NewTec-GmbH/esp32-can-iot/Coding/fw/doc/Media/EnvironmentDiagram.png

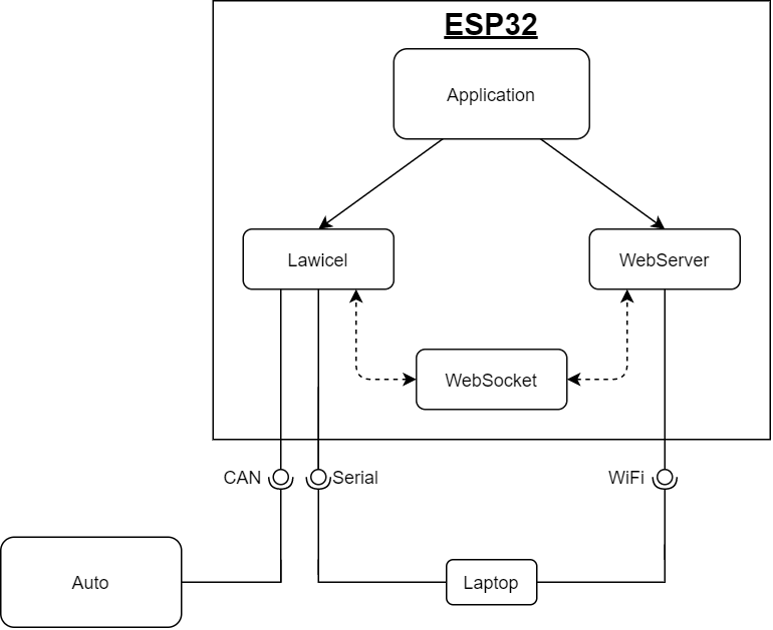
Coding/fw/doc/Media/EnvironmentDiagram.png
