NewTec-GmbH/esp32-can-iot/Coding/fw/doc/Media/HW_Case2.png

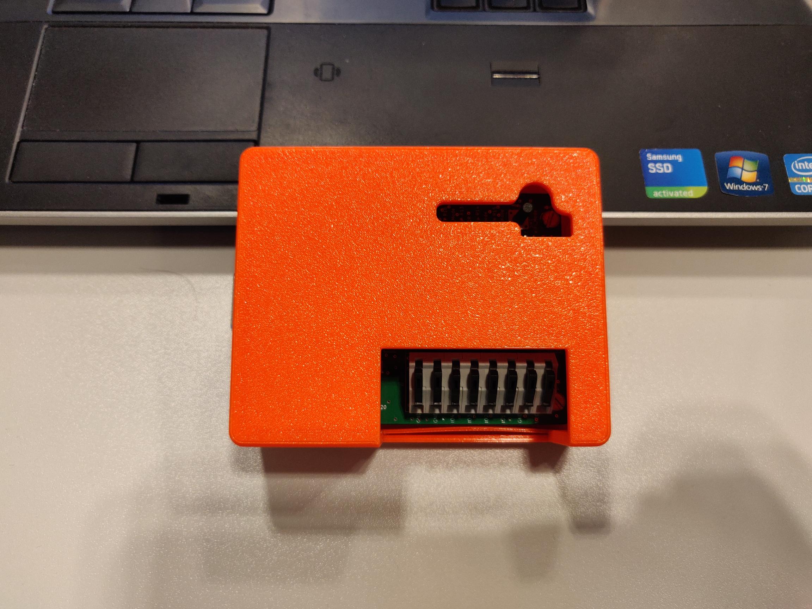
Coding/fw/doc/Media/HW_Case2.png
