NewTec-GmbH/esp32-can-iot/Coding/fw/doc/Media/HW_Case3.png

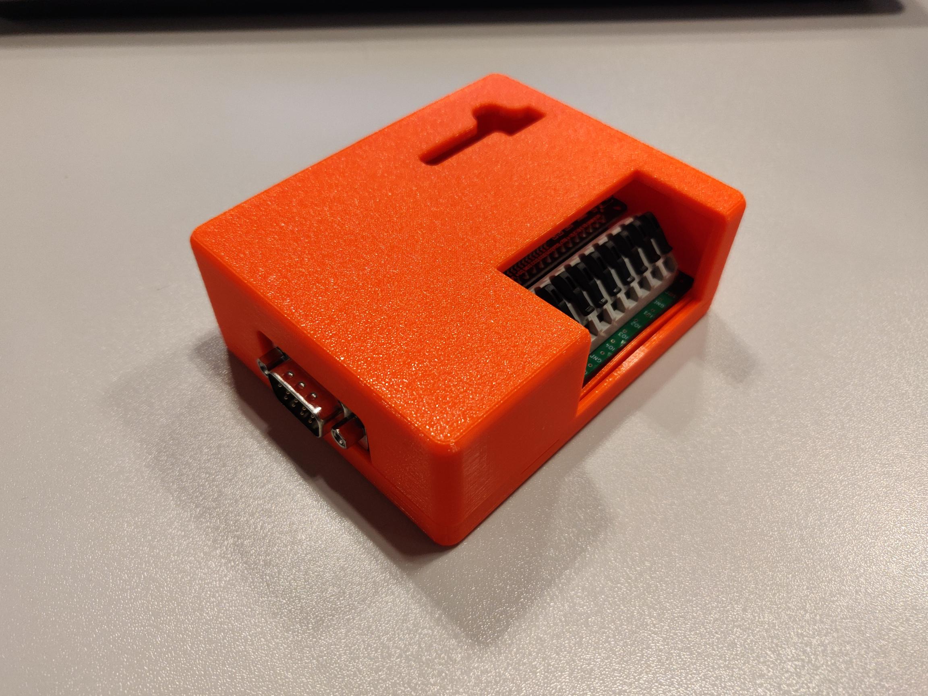
Coding/fw/doc/Media/HW_Case3.png
