NewTec-GmbH/esp32-can-iot/Coding/fw/doc/Media/HW_Final4.JPG

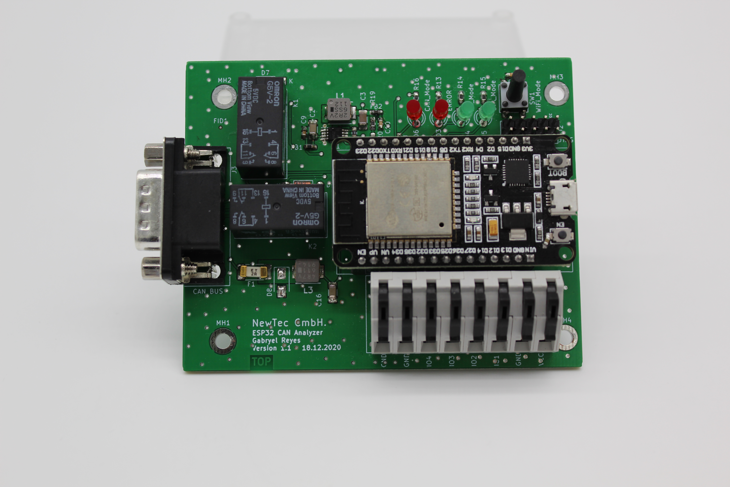
Coding/fw/doc/Media/HW_Final4.JPG
